fahroniganteng/Arduino-esp8266-mini-JWS/code/MD_MAX72xx_pix.cpp

/*
MD_MAX72xx - Library for using a MAX7219/7221 LED matrix controller

See header file for comments

This file contains methods that act on the matrix as a pixel field,
generally only acting on the visible device range of the buffered
device field (ie, the physical pixel matrix).

Copyright (C) 2012-14 Marco Colli. All rights reserved.

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
You should have received a copy of the GNU Lesser General Public
License along with this library; if not, write to the Free Software
Foundation, Inc., 51 Franklin St, Fifth Floor, Boston, MA 02110-1301 USA
 */
#include <Arduino.h>
#include "MD_MAX72xx.h"
#include "MD_MAX72xx_lib.h"

/**
 * \file
 * \brief Implements pixel related methods
 */

void MD_MAX72XX::clear(uint8_t startDev, uint8_t endDev)
{
  if (endDev < startDev) return;

  for (uint8_t buf = startDev; buf <= endDev; buf++)
  {
    memset(_matrix[buf].dig, 0, sizeof(_matrix[buf].dig));
    _matrix[buf].changed = ALL_CHANGED;
  }

  if (_updateEnabled) flushBufferAll();
}

bool MD_MAX72XX::getBuffer(uint16_t col, uint8_t size, uint8_t *pd)
{
  if ((col >= getColumnCount()) || (pd == NULL))
    return(false);

  for (uint8_t i=0; i<size; i++)
    *pd++ = getColumn(col--);

  return(true);
}

bool MD_MAX72XX::setBuffer(uint16_t col, uint8_t size, uint8_t *pd)
{
  bool b = _updateEnabled;

  if ((col >= getColumnCount()) || (pd == NULL))
    return(false);

  _updateEnabled = false;
  for (uint8_t i=0; i<size; i++)
    setColumn(col--, *pd++);
  _updateEnabled = b;

  if (_updateEnabled) flushBufferAll();

  return(true);
}

bool MD_MAX72XX::getPoint(uint8_t r, uint16_t c)
{
  uint8_t buf = c/COL_SIZE;

  c %= COL_SIZE;
  PRINT("\ngetPoint: (", buf);
  PRINT(", ", r);
  PRINT(", ", c);
  PRINTS(")");

  if ((buf > LAST_BUFFER) || (r >= ROW_SIZE) || (c >= COL_SIZE))
    return(false);

  if (_hwDigRows)
    return(bitRead(_matrix[buf].dig[HW_ROW(r)], HW_COL(c)) == 1);
  else
    return(bitRead(_matrix[buf].dig[HW_ROW(c)], HW_COL(r)) == 1);
}

bool MD_MAX72XX::setPoint(uint8_t r, uint16_t c, bool state)
{
  uint8_t buf = c/COL_SIZE;
  c %= COL_SIZE;

  PRINT("\nsetPoint: (", buf);
  PRINT(", ", r);
  PRINT(", ", c);
  PRINT(") = ", state?1:0);

  if ((buf > LAST_BUFFER) || (r >= ROW_SIZE) || (c >= COL_SIZE))
    return(false);

  if (state)
  {
    if (_hwDigRows)
      bitSet(_matrix[buf].dig[HW_ROW(r)], HW_COL(c));
    else
      bitSet(_matrix[buf].dig[HW_ROW(c)], HW_COL(r));
  }
  else
  {
    if (_hwDigRows)
      bitClear(_matrix[buf].dig[HW_ROW(r)], HW_COL(c));
    else
      bitClear(_matrix[buf].dig[HW_ROW(c)], HW_COL(r));
  }

  if (_hwDigRows)
    bitSet(_matrix[buf].changed, HW_ROW(r));
  else
    bitSet(_matrix[buf].changed, HW_ROW(c));

  if (_updateEnabled) flushBuffer(buf);

  return(true);
}

bool MD_MAX72XX::setRow(uint8_t startDev, uint8_t endDev, uint8_t r, uint8_t value)
{
  bool b = _updateEnabled;

  PRINT("\nsetRow: ", r);

  if ((r >= ROW_SIZE) || (endDev < startDev))
    return(false);

  _updateEnabled = false;
  for (uint8_t i = startDev; i <= endDev; i++)
    setRow(i, r, value);
  _updateEnabled = b;

  if (_updateEnabled) flushBufferAll();

  return(true);
}

bool MD_MAX72XX::transform(uint8_t startDev, uint8_t endDev, transformType_t ttype)
{
 // uint8_t t[ROW_SIZE];
  uint8_t colData;
  bool b = _updateEnabled;

  if (endDev < startDev) return(false);

  _updateEnabled = false;

  switch (ttype)
  {
    case TSL: // Transform Shift Left one pixel element (with overflow)
    colData = 0;
    // if we can call the user function later then we don't need to do anything here
    // however, wraparound mode means we know the data so no need to request from the
    // callback at all - just save it for later
    if (_wrapAround)
      colData = getColumn(((endDev+1)*COL_SIZE)-1);
    else if (_cbShiftDataOut != NULL)
      (*_cbShiftDataOut)(endDev, ttype, getColumn(((endDev+1)*COL_SIZE)-1));

    // shift all the buffers along
    for (int8_t buf = endDev; buf >= startDev; --buf)
    {
      transformBuffer(buf, ttype);
      // handle the boundary condition
      setColumn(buf, 0, getColumn(buf-1, COL_SIZE-1));
    }

    // if we have a callback function, now is the time to get the data if we are
    // not in wraparound mode
    if (_cbShiftDataIn != NULL && !_wrapAround)
      colData = (*_cbShiftDataIn)(startDev, ttype);

    setColumn((startDev*COL_SIZE), colData);
    break;

    case TSR: // Transform Shift Right one pixel element (with overflow)
    // if we can call the user function later then we don't need to do anything here
    // however, wraparound mode means we know the data so no need to request from the
    // callback at all - just save it for later.
    colData = 0;
    if (_wrapAround)
      colData = getColumn(startDev*COL_SIZE);
    else if (_cbShiftDataOut != NULL)
      (*_cbShiftDataOut)(startDev, ttype, getColumn((startDev*COL_SIZE)));

    // shift all the buffers along
    for (uint8_t buf=startDev; buf<=endDev; buf++)
    {
      transformBuffer(buf, ttype);

      // handle the boundary condition
      setColumn(buf, COL_SIZE-1, getColumn(buf+1, 0));
    }

    // if we have a callback function, now is the time to get the data if we are
    // not in wraparound mode
    if (_cbShiftDataIn != NULL && !_wrapAround)
      colData = (*_cbShiftDataIn)(endDev, ttype);

    setColumn(((endDev+1)*COL_SIZE)-1, colData);
    break;

    case TFLR: // Transform Flip Left to Right (use the whole field)
    // first reverse the device buffers end for end
    for (uint8_t buf = 0; buf < (endDev - startDev)/2; buf++)
    {
      deviceInfo_t	t;

      t = _matrix[startDev + buf];
      _matrix[startDev + buf] = _matrix[endDev - buf];
      _matrix[endDev - buf] = t;
    }

    // now reverse the columns in each device
    for (uint8_t buf = startDev; buf <= endDev; buf++)
      transformBuffer(buf, ttype);
    break;

    // These next transformations work the same just by doing the individual devices
    case TSU:   // Transform Shift Up one pixel element
    case TSD:   // Transform Shift Down one pixel element
    case TFUD:  // Transform Flip Up to Down
    case TRC:   // Transform Rotate Clockwise
    case TINV:  // Transform INVert
    for (uint8_t buf = startDev; buf <= endDev; buf++)
      transformBuffer(buf, ttype);
    break;

    default:
      return(false);
  }

  _updateEnabled = b;

  if (_updateEnabled) flushBufferAll();

  return(true);
}
